ikeefe12/tankervision-pdb/firmware/board_control_test/results/charger-2026-09-14/hardware-final.png

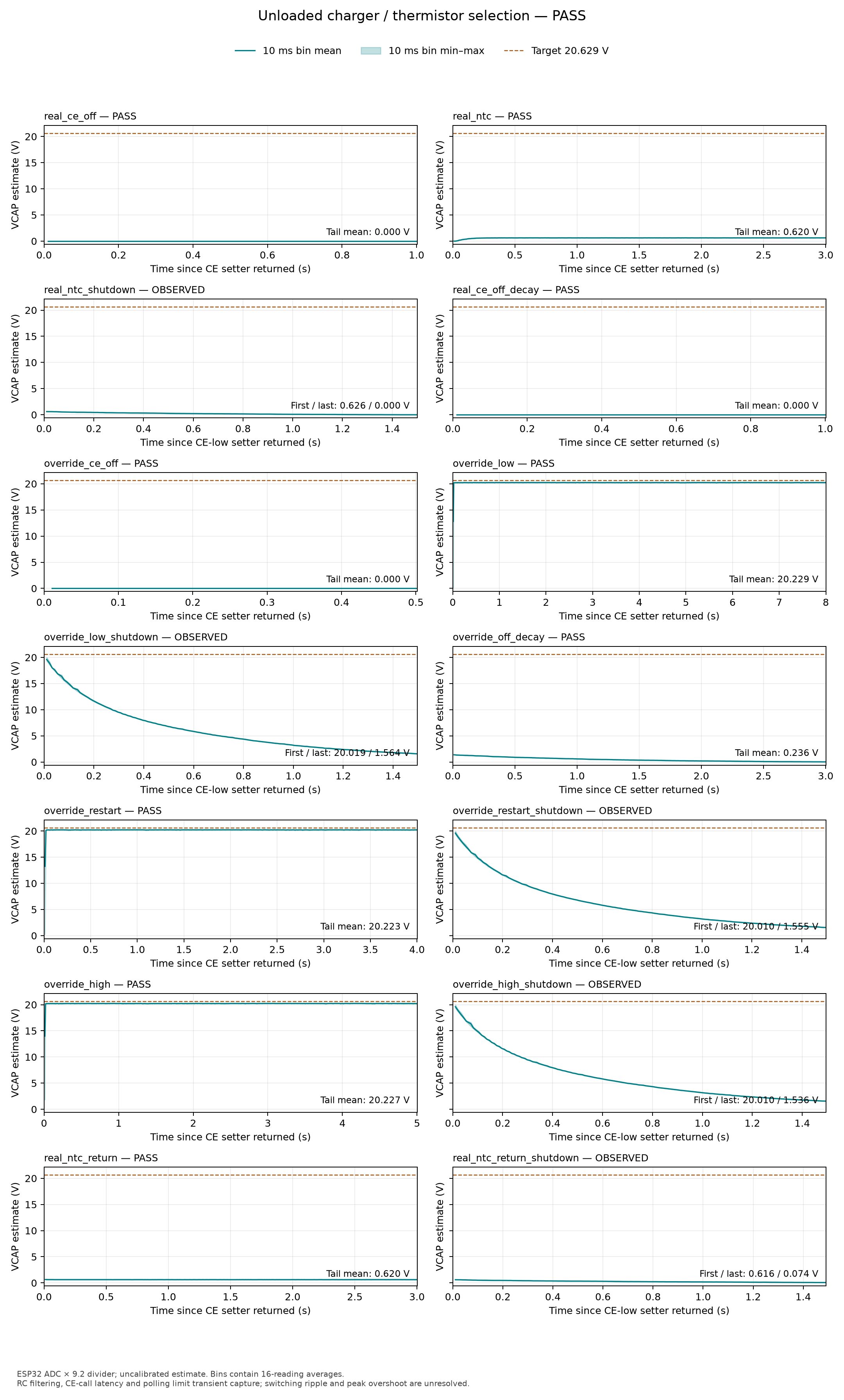
firmware/board_control_test/results/charger-2026-09-14/hardware-final.png
