ikeefe12/tankervision-pdb/firmware/board_control_test/results/transfer-2026-09-14/voltage.csv

host_utc | session | seq | t | state | VCAP | TS_mV | MAIN | USB | DC | CAP | SS | OUT | EN42 | LED | backup_ms
2026-09-14T21:31:25.507768+00:00 | 0B958541 | 1 | 905 | STOPPED | 0.0000 | 1933 | 1 | 1 | 0 | 0 | 1 | 0x00 | 0 | 0 | 0
2026-09-14T21:31:25.607532+00:00 | 0B958541 | 2 | 1006 | STOPPED | 0.0000 | 1934 | 1 | 1 | 0 | 0 | 1 | 0x00 | 0 | 0 | 0
2026-09-14T21:31:26.608466+00:00 | 0B958541 | 3 | 2007 | STOPPED | 0.0000 | 1934 | 1 | 1 | 0 | 0 | 1 | 0x00 | 0 | 0 | 0
2026-09-14T21:31:27.609561+00:00 | 0B958541 | 4 | 3008 | STOPPED | 0.0000 | 1933 | 1 | 1 | 0 | 0 | 1 | 0x00 | 0 | 0 | 0
2026-09-14T21:31:28.610564+00:00 | 0B958541 | 5 | 4009 | STOPPED | 0.0000 | 1935 | 1 | 1 | 0 | 0 | 1 | 0x00 | 0 | 0 | 0
2026-09-14T21:31:30.220762+00:00 | 0B958541 | 6 | 5619 | CHARGING | 0.0000 | 1934 | 1 | 1 | 0 | 0 | 1 | 0x03 | 0 | 0 | 0
2026-09-14T21:31:31.220436+00:00 | 0B958541 | 7 | 6619 | CHARGING | 0.1840 | 1935 | 1 | 1 | 0 | 0 | 1 | 0x03 | 0 | 0 | 0
2026-09-14T21:31:33.220473+00:00 | 0B958541 | 8 | 7619 | CHARGING | 0.3956 | 1934 | 1 | 1 | 0 | 0 | 1 | 0x03 | 0 | 0 | 0
2026-09-14T21:31:33.221090+00:00 | 0B958541 | 9 | 8619 | CHARGING | 0.6256 | 1934 | 1 | 1 | 0 | 0 | 1 | 0x03 | 0 | 0 | 0
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
